Phunkafizer/AllSerial/2_RS485_RS422/2_RS485_RS422_BOARD 3D.jpg

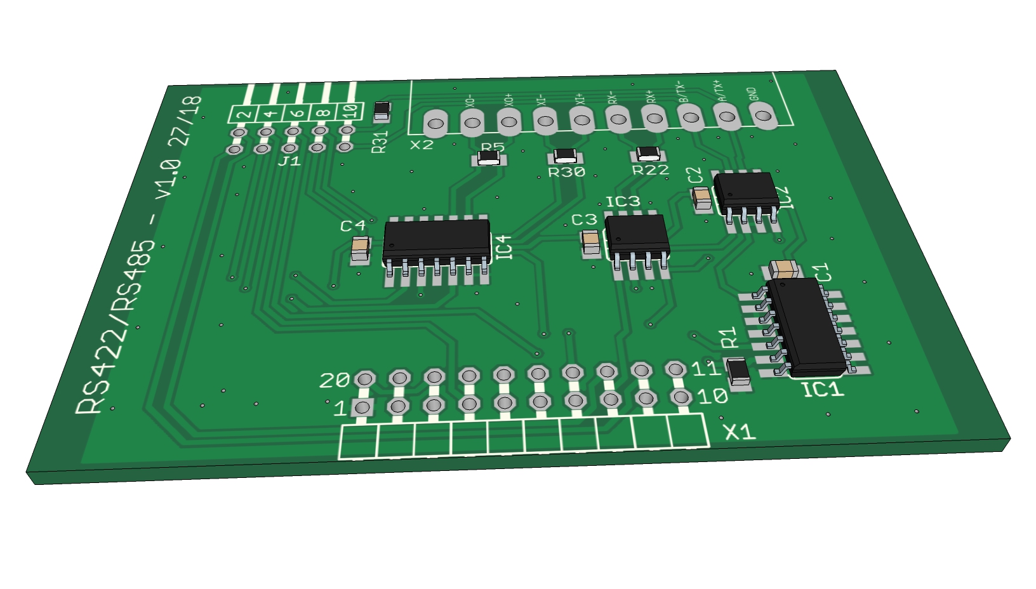
2_RS485_RS422/2_RS485_RS422_BOARD 3D.jpg
