Phunkafizer/AllSerial/4_TTL/4_TTL_SCHEM.pdf

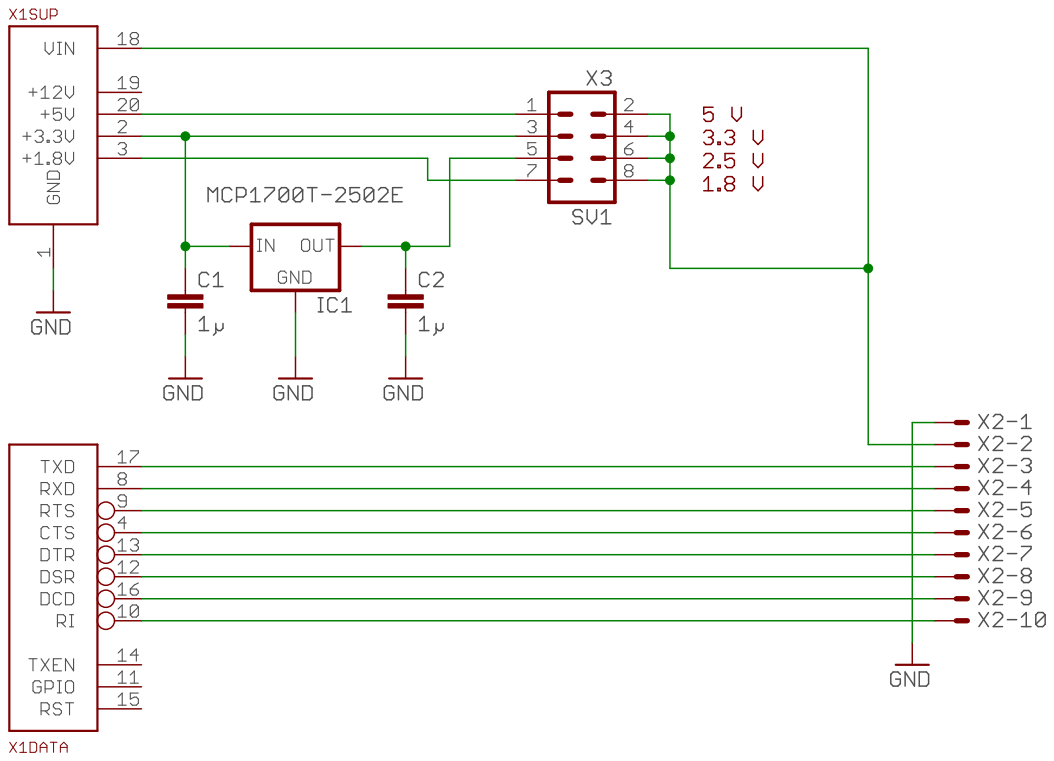
[picture p41: page 1]
