Phunkafizer/AllSerial/5_TTY/5_TTY_SCHEM.pdf

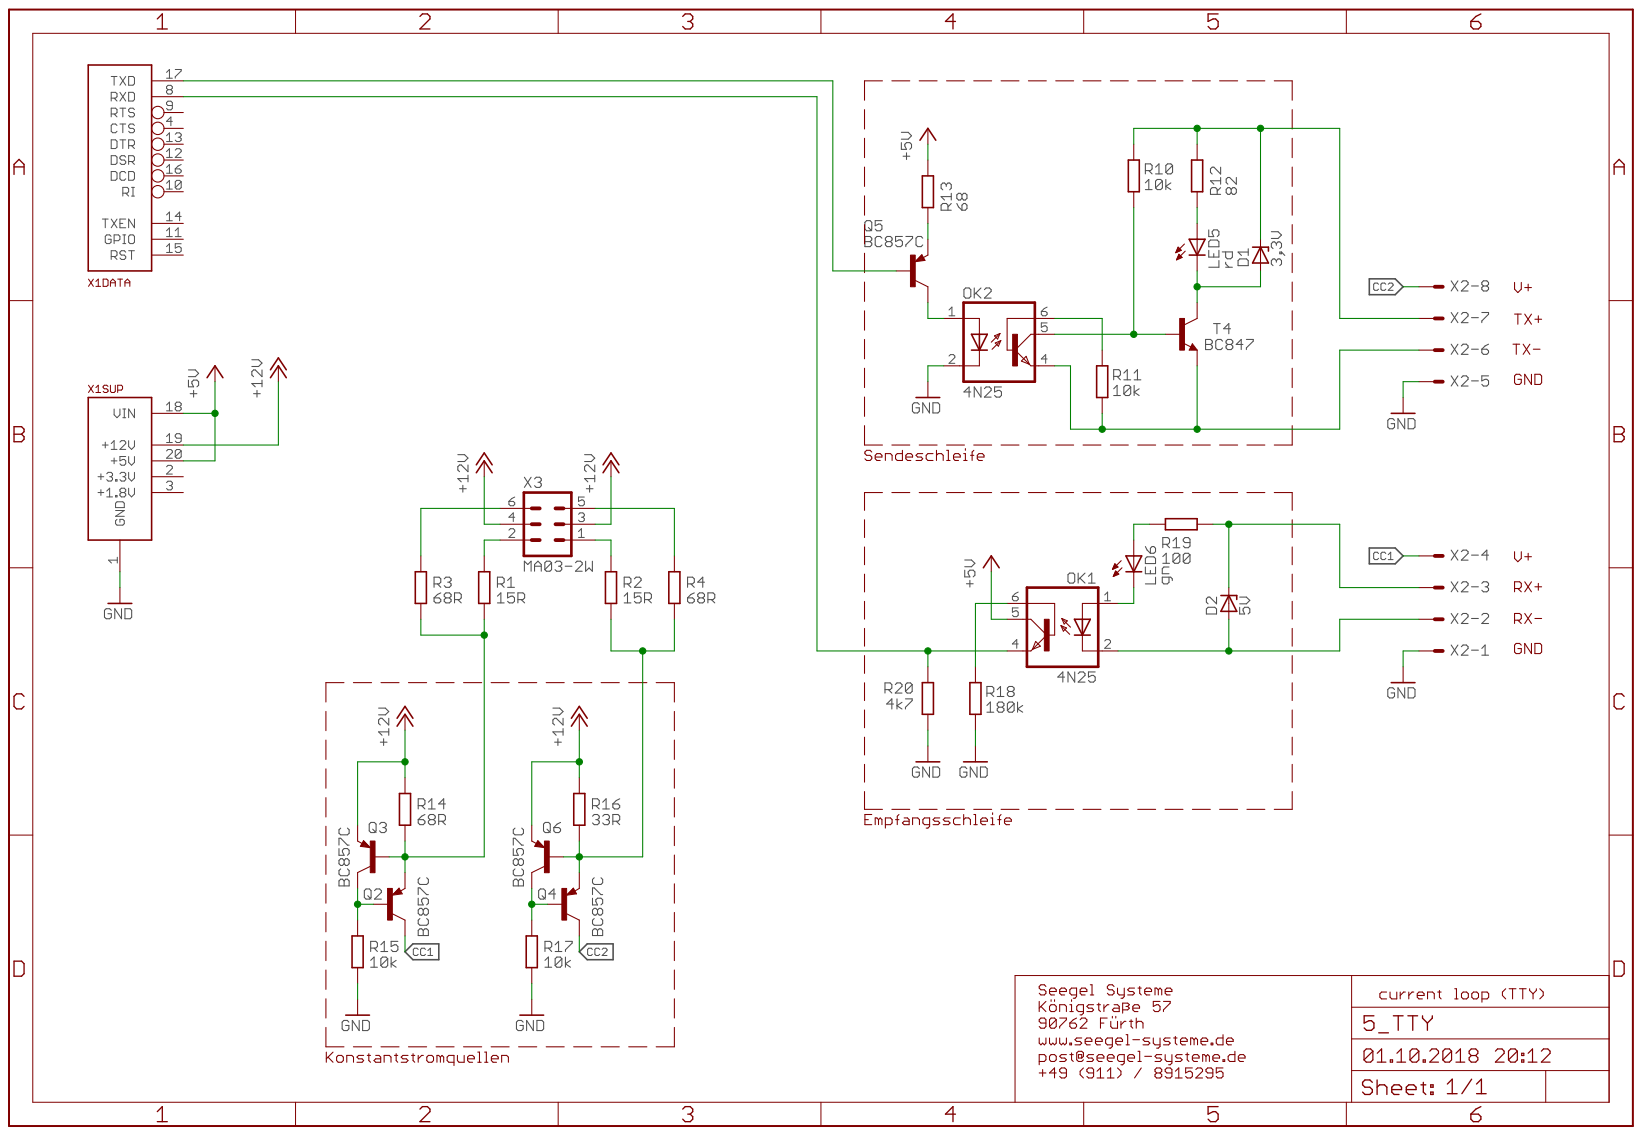
[picture p42: page 1]
