Phunkafizer/AllSerial/6_LIN/6_LIN_ASSEM.pdf

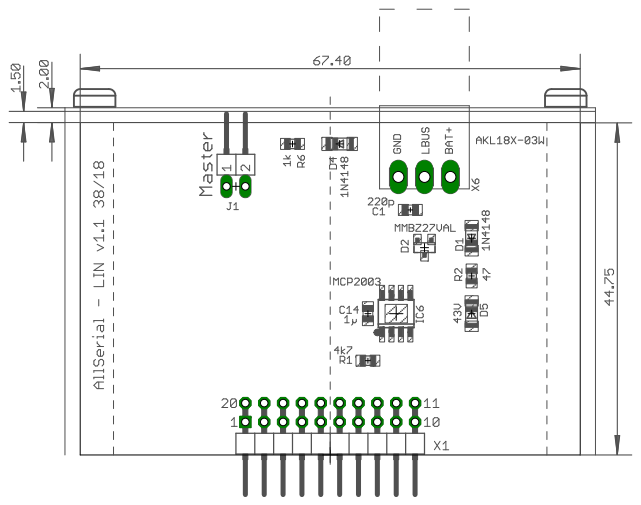
[picture p43: page 1]
