Phunkafizer/AllSerial/6_LIN/6_LIN_SCHEM.pdf

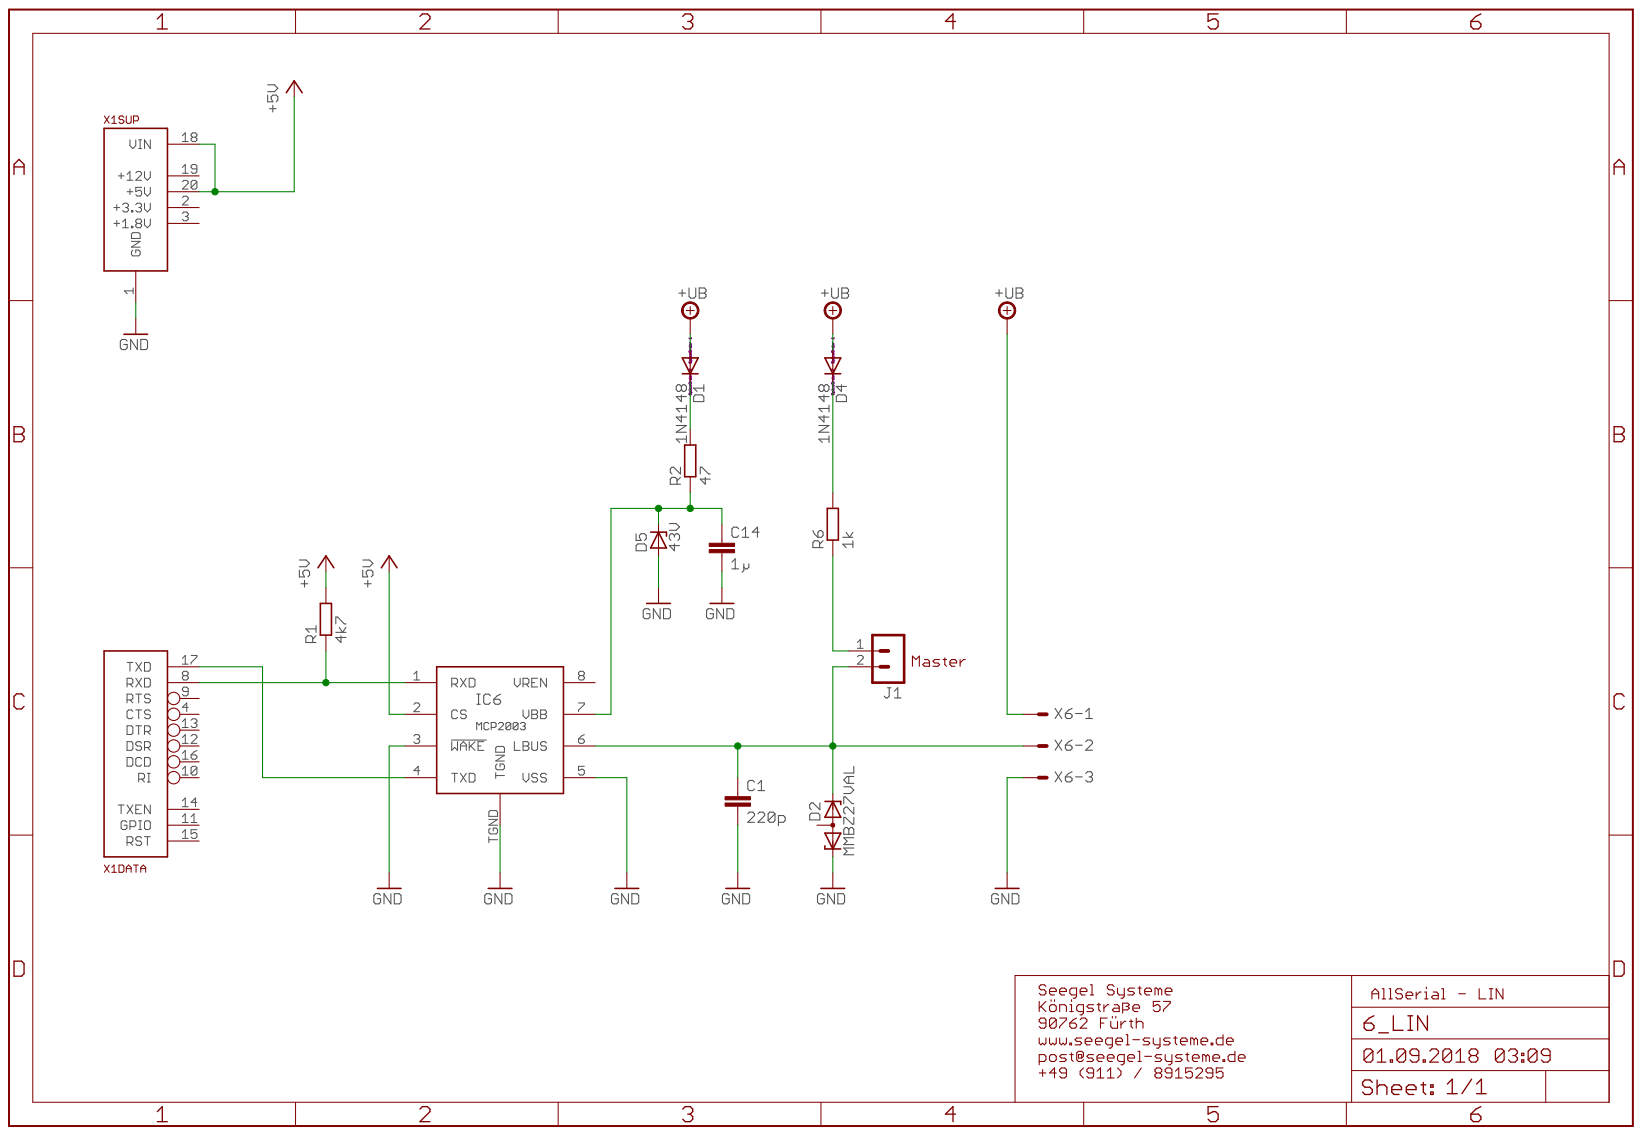
[picture p44: page 1]
