Phunkafizer/AllSerial/5_TTY/5_TTY_ASSEM.pdf

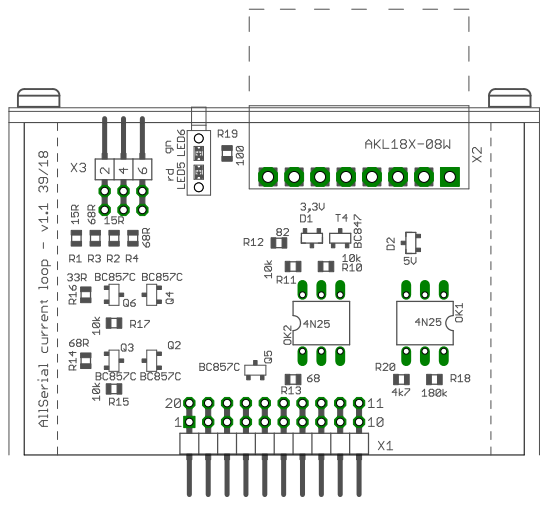
[picture p45: page 1]
