Phunkafizer/AllSerial/2_RS485_RS422/2_RS485_RS422_ASSEM.pdf

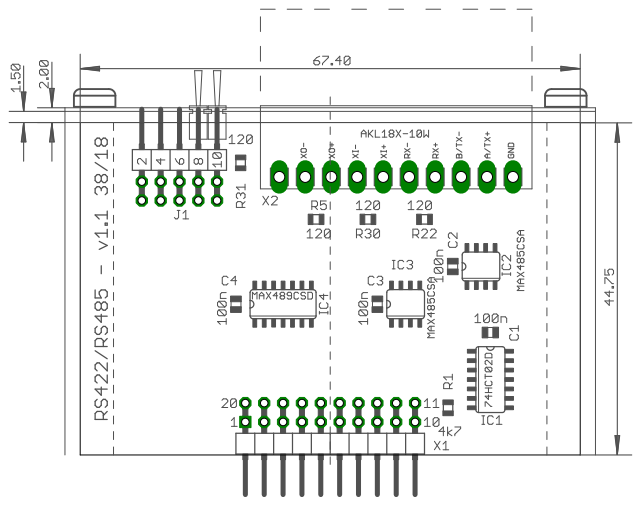
[picture p46: page 1]
