Phunkafizer/AllSerial/1A_MAIN_FTDI/1A_Main_Schem.pdf

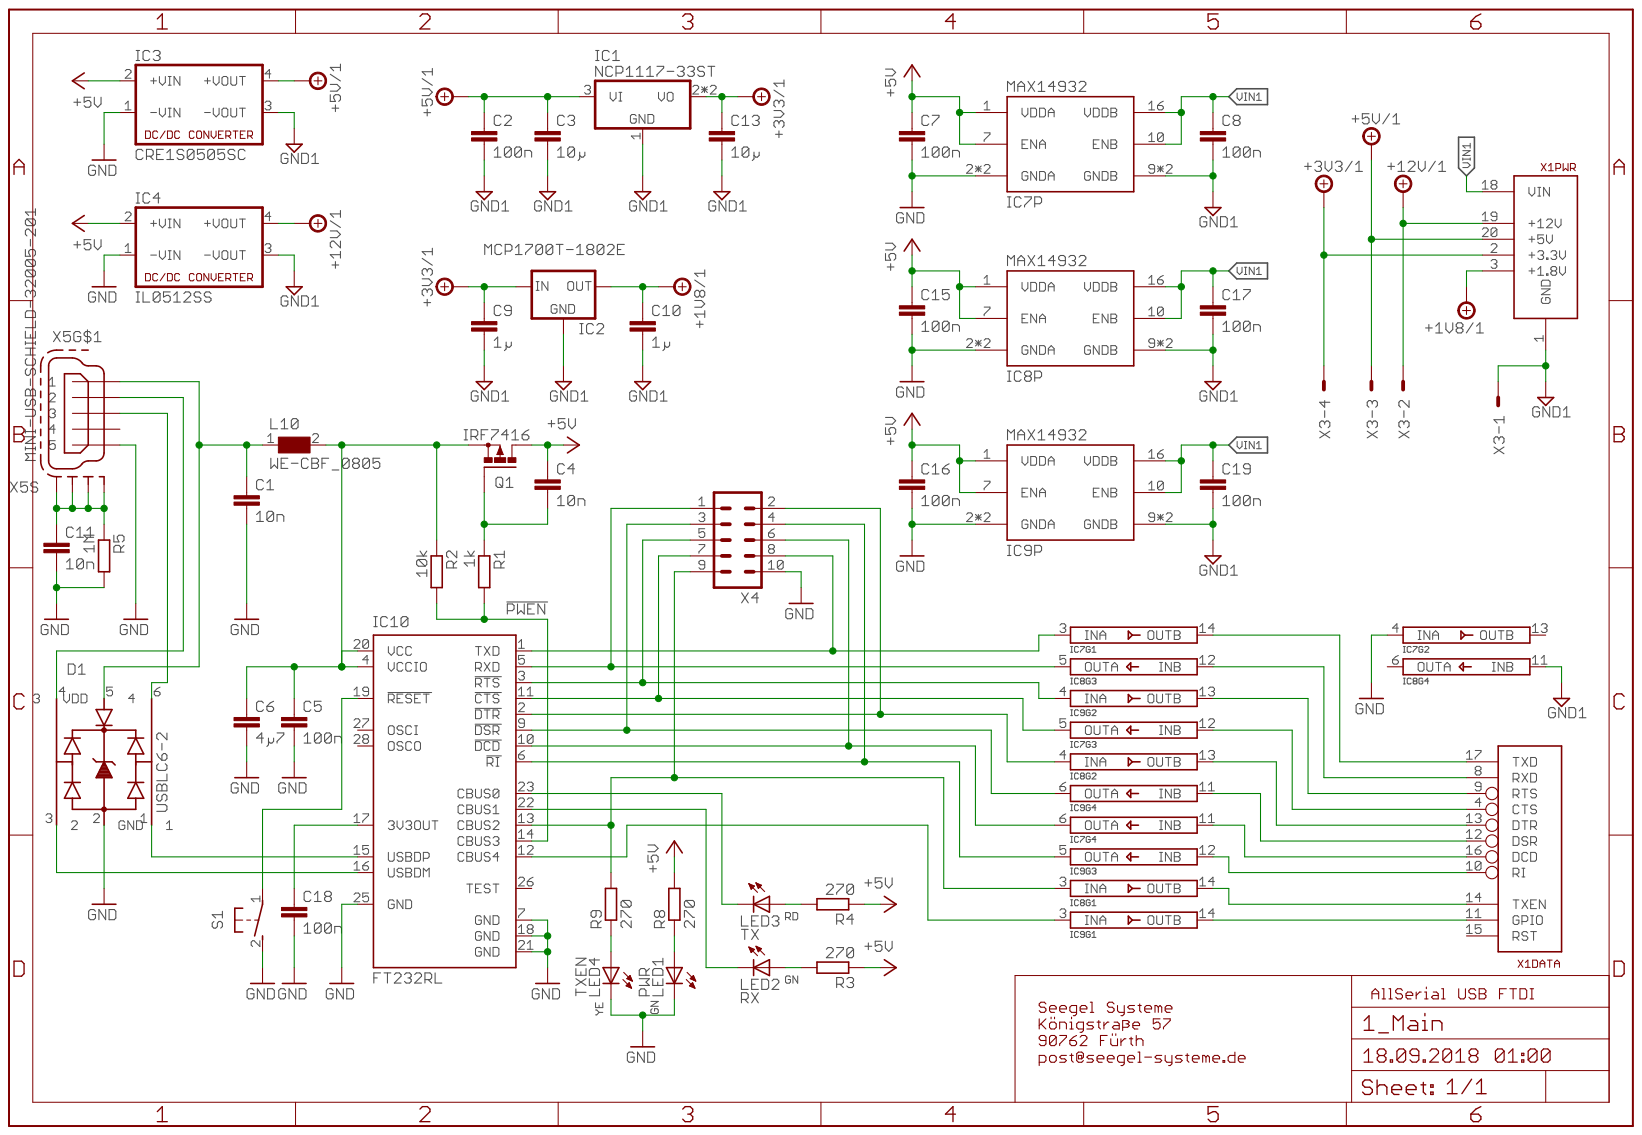
[picture p47: page 1]
