Phunkafizer/AllSerial/2_RS485_RS422/2_RS485_RS422.pdf

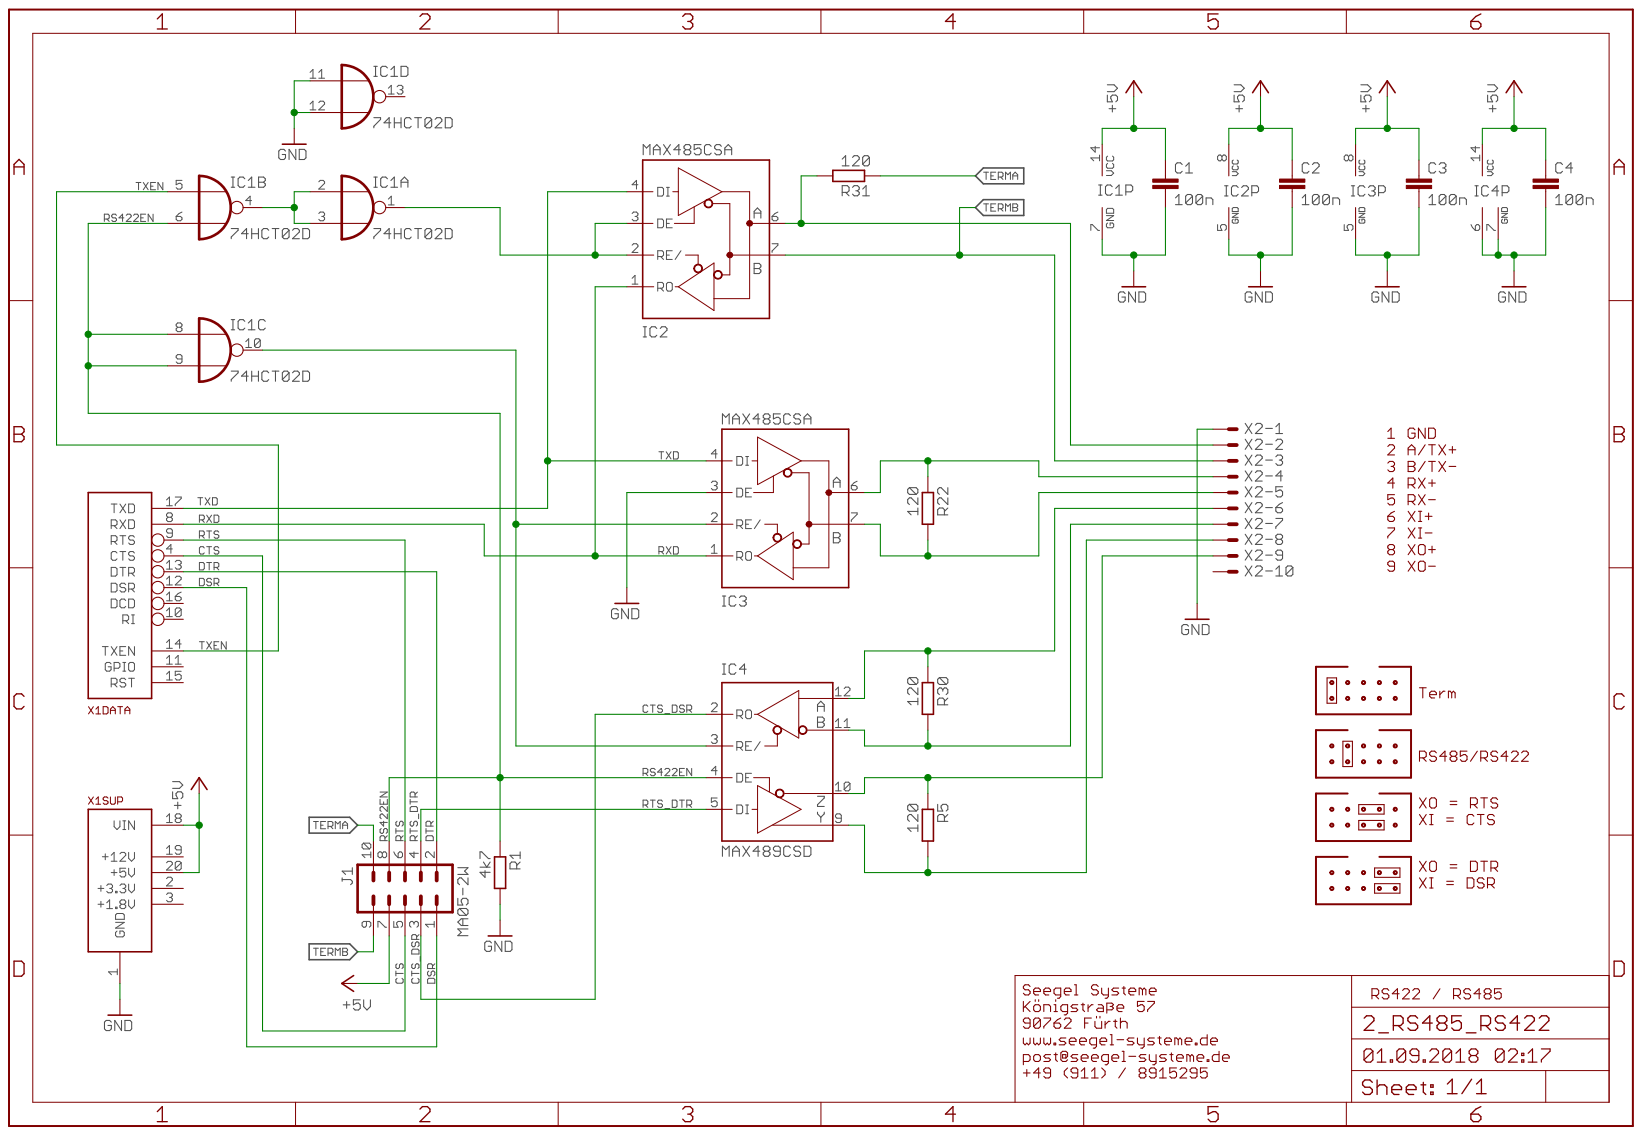
[picture p48: page 1]
